SonuSwaroopRaj/BAHA-Vehicle-AutoCAD-Files/BRAKE DESIGN/BRAKE 1/DISK BRAKE.JPG

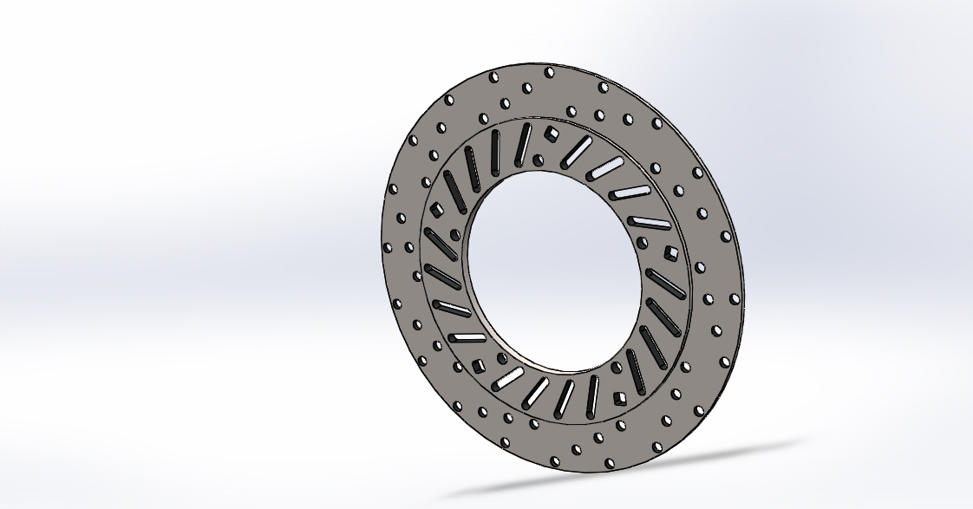
BRAKE DESIGN/BRAKE 1/DISK BRAKE.JPG
