SonuSwaroopRaj/BAHA-Vehicle-AutoCAD-Files/BRAKE DESIGN/BRAKE 2/View (2).png

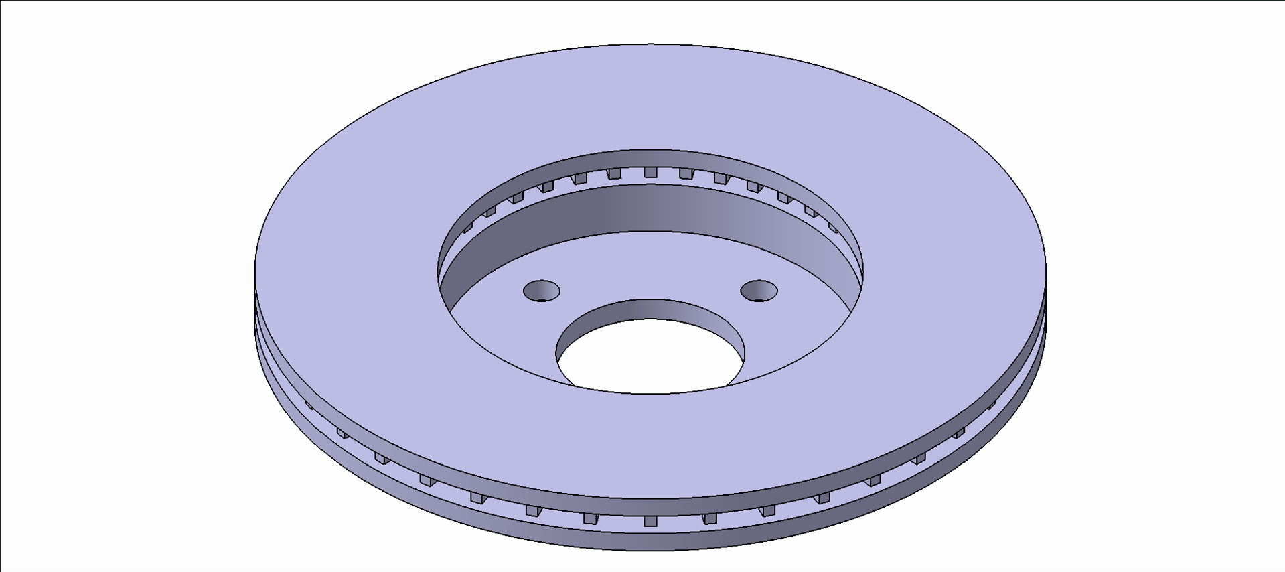
BRAKE DESIGN/BRAKE 2/View (2).png
